ansemjo/luftctl/images/PXL_20220126_231922923.jpg

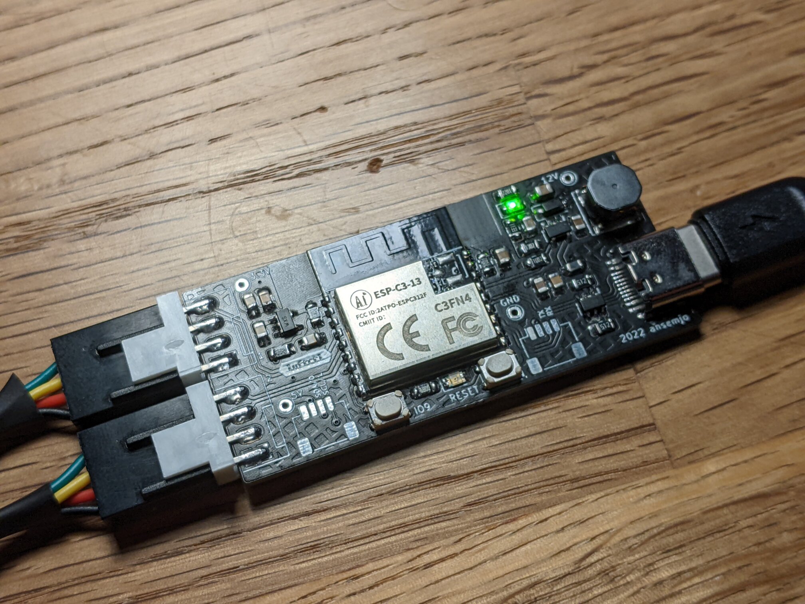
images/PXL_20220126_231922923.jpg
